JhonVelasquez/Embedded_system_Synchronize_Plant/Diagrams/RTOS_Flowchats_Architecture_diagrams/Flowchart_of_task_t_FG2_t_FG3.png

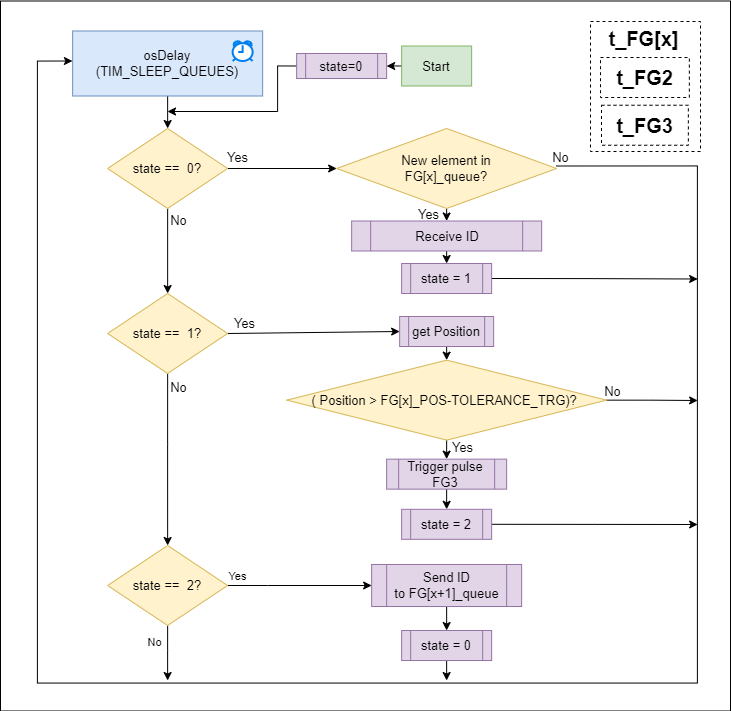
Diagrams/RTOS_Flowchats_Architecture_diagrams/Flowchart_of_task_t_FG2_t_FG3.png
