JhonVelasquez/Embedded_system_Synchronize_Plant/Diagrams/RTOS_Flowchats_Architecture_diagrams/Flowchart_of_task_t_RPI.png

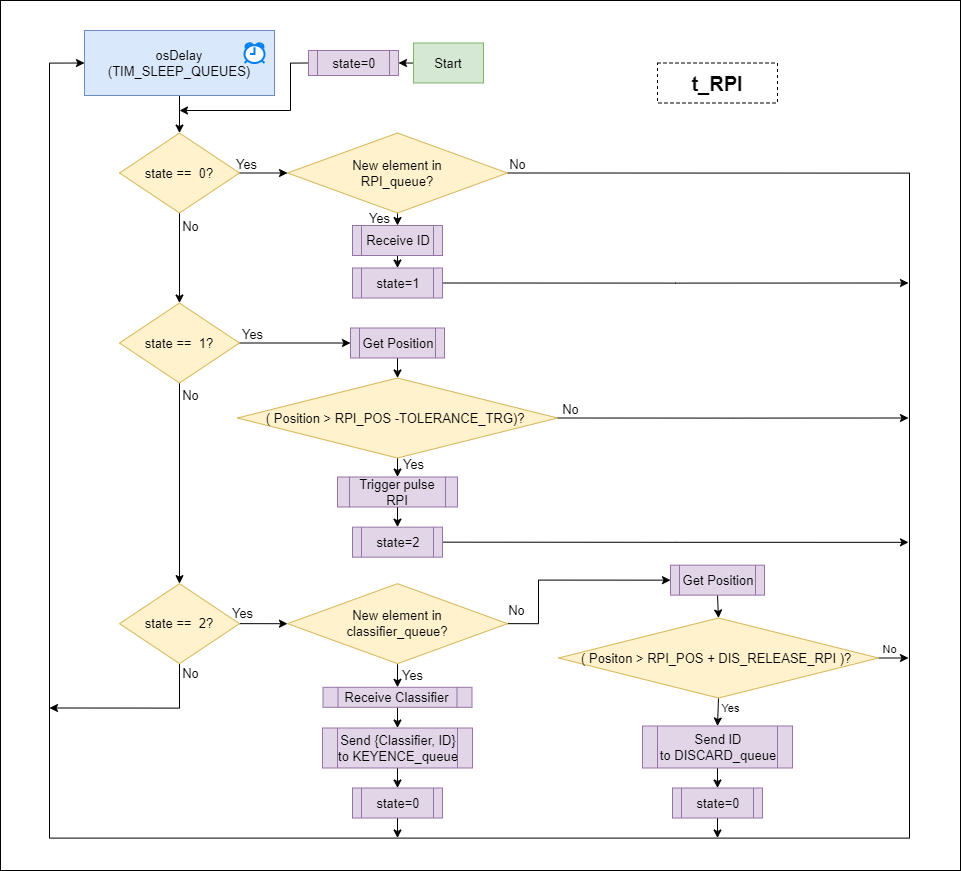
Diagrams/RTOS_Flowchats_Architecture_diagrams/Flowchart_of_task_t_RPI.png
