JhonVelasquez/Embedded_system_Synchronize_Plant/Diagrams/RTOS_Flowchats_Architecture_diagrams/RTOS_Command_Line_Interface_architechture.png

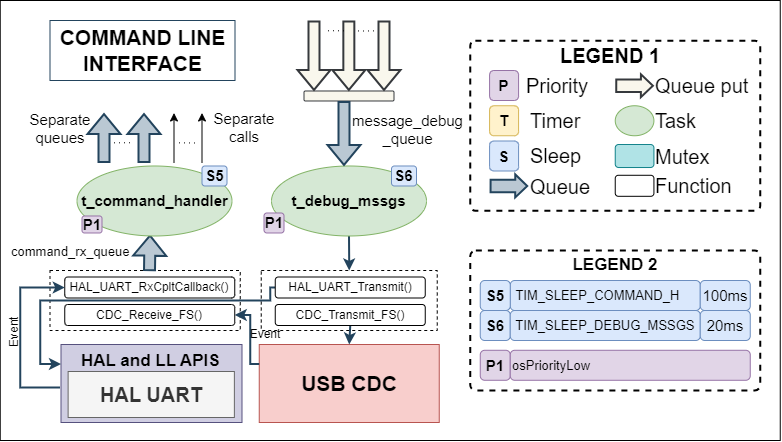
Diagrams/RTOS_Flowchats_Architecture_diagrams/RTOS_Command_Line_Interface_architechture.png
