JhonVelasquez/Embedded_system_Synchronize_Plant/KICAD_Schematich/jv_thesis/Ethernet_STM32_v1.png

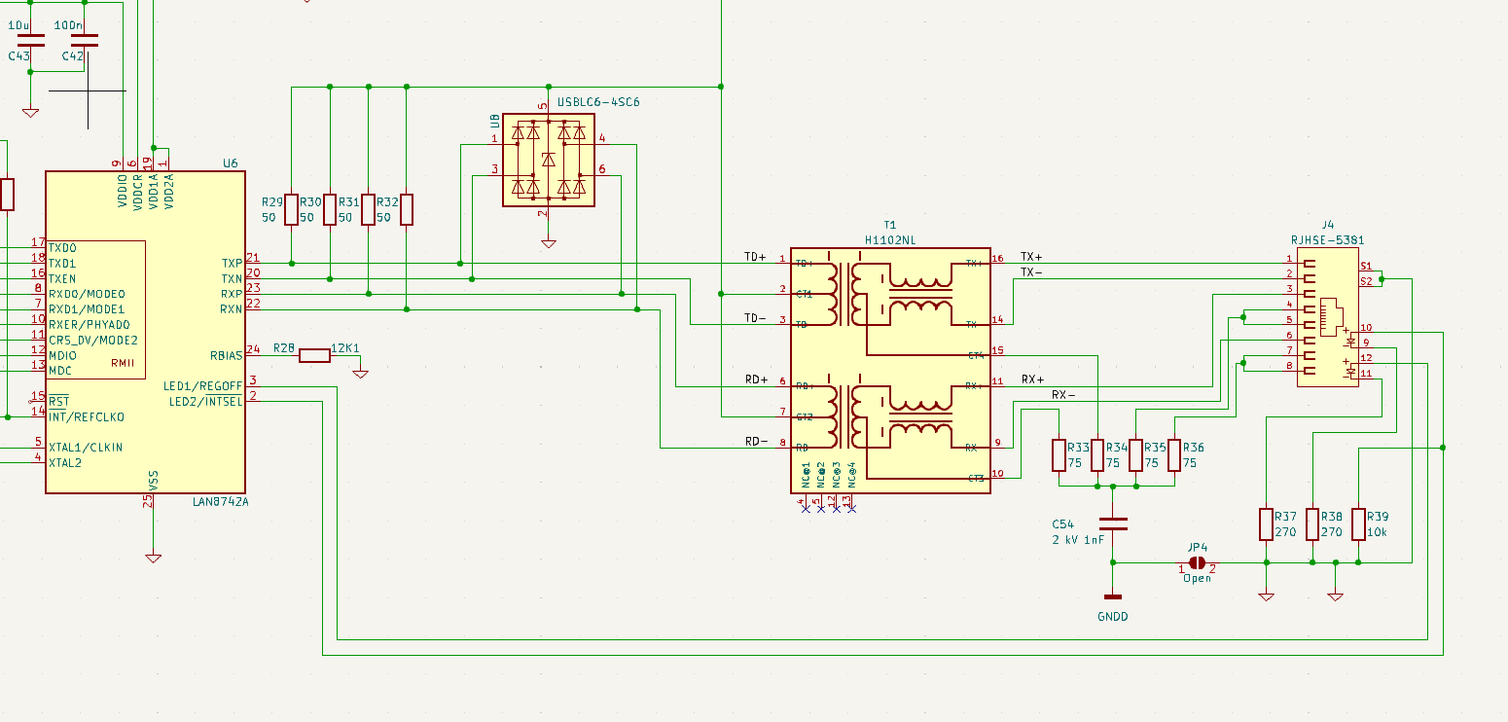
KICAD_Schematich/jv_thesis/Ethernet_STM32_v1.png
