JhonVelasquez/Embedded_system_Synchronize_Plant/KICAD_Schematich/jv_thesis/jv_thesis.kicad_sch

## KiCad design KICAD_Schematich/jv_thesis/jv_thesis.kicad_sch (2023-09-27)

Schematic: jv_thesis.kicad_sch

Parts:
C1, C2, C3, C4, C5, C6, C7, C8, C9, C10, C11, C12, C14, C27, C29, C42, C46, C47, C48, C49, C50, C51, C53, C54, C55, C59, C60, C63: 100n; C_0805_2012Metric_Pad1.18x1.45mm_HandSolder
C13, C30, C43, C58, C64: 10u; C_0805_2012Metric_Pad1.18x1.45mm_HandSolder
C15, C18, C28, C45, C56, C61, C62: 1u; C_0805_2012Metric_Pad1.18x1.45mm_HandSolder
C16, C17: 2.2u; C_0805_2012Metric_Pad1.18x1.45mm_HandSolder
C31, C41: 16p; CBR06C160F5GAC
C32, C40: 30p; CAP_600S0R1AT250XT_ATC
C33, C35, C36, C39: 10u-pol; CP_EIA-3216-18_Kemet-A_Pad1.58x1.35mm_HandSolder
C34: 20u (25v)-pol; CP_Elec_8x6.2
C37: 1u; C_1206_3216Metric_Pad1.33x1.80mm_HandSolder
C38: 4.7u; C_1812_4532Metric_Pad1.57x3.40mm_HandSolder
C44: 470p; C_0805_2012Metric_Pad1.18x1.45mm_HandSolder
CRYSTAL1: ECS-80-18-33-JGN-TR
CRYSTAL2: SXT21422AA07-25.000MT; SXT21422AA07_25_000M; PARTREV N/A
D1, D2, D3, D6: L_GREEN; D_0805_2012Metric_Pad1.15x1.40mm_HandSolder
D4: BAT60A; D_SOD-323_HandSoldering
D5: L_RED; D_0805_2012Metric_Pad1.15x1.40mm_HandSolder
D7: L_BLUE; D_0805_2012Metric_Pad1.15x1.40mm_HandSolder
F1: ERBRG2R50V; Fuse_1206_3216Metric_Pad1.42x1.75mm_HandSolder
FB1, FB2: 120R; L_0805_2012Metric_Pad1.15x1.40mm_HandSolder
H1, H2, H3, H4: MH; MountingHole_3.2mm_M3_Pad_Via
J1: 10118194-0001LF; USB_Micro_B_Female_10118194-0001LF; MPN 10118194-0001LF; Digi-Key_PN 609-4618-1-ND
J2, J5, J7, J8: Conn_01x02; PinSocket_1x02_P2.54mm_Vertical
J3: Conn_01x06; PinSocket_1x06_P2.54mm_Vertical
J4, J6: Conn_02x03; PinSocket_2x03_P2.54mm_Vertical
J9: 2000-1-2-41-00-BK; HDMI_A_Female_2000-1-2-41-00-BK; MPN 2000-1-2-41-00-BK; Digi-Key_PN 1175-1703-ND
J10: USB-A1HSB6
J11: THD-20-R; PinHeader_2x20_P2.54mm_Vertical; Part Description PinHeader_2x20_P2.54mm_Vertical
J12: ARJM11C7-502-AB-ER2-T; PARTREV 04.22.2019
J13: Keyence_1; 284512-2
J14: Keyence_2; 284512-2
J15: Keyence_3; 284512-2
J16: Keyence_4; 284512-2
J17, J18, J19: Conn_01x03; TerminalBlock_MetzConnect_Type059_RT06303HBWC_1x03_P3.50mm_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
J20, J21, J22, J27, J28: 284512-2
J23: Keyence_5; 284512-2
J24, J29, J30: Keyence_6; 284512-2
J25: Power_24V; 284512-2
J31: Conn_01x03; PinHeader_1x03_P2.54mm_Vertical
JP1, JP2, JP3, JP4, JP5, JP6, JP7, JP13, JP14, JP16, JP19, JP20, JP21, JP22, JP23, JP24, JP25, JP26, JP27, JP28, JP29, JP30: Open; SolderJumper-2_P1.3mm_Open_RoundedPad1.0x1.5mm
JP8, JP9, JP10, JP15, JP18: Closed; SolderJumper-2_P1.3mm_Bridged_RoundedPad1.0x1.5mm
Module1: ComputeModule4-CM4; Raspberry-Pi-4-Compute-Module
Q1: BC847; SOT-323_SC-70_Handsoldering
R1, R6, R33, R87: 10k; R_0805_2012Metric_Pad1.20x1.40mm_HandSolder
R2, R3, R36, R38, R40, R41, R49, R50, R51, R52, R57, R58, R59, R60, R68, R69, R74, R77: 2.2k; R_0805_2012Metric_Pad1.20x1.40mm_HandSolder
R4, R35, R39, R42, R43, R45, R46, R47, R48, R53, R54, R55, R56, R63, R64, R65, R66, R67: 210; R_0805_2012Metric_Pad1.20x1.40mm_HandSolder
R5: 1K; R_0805_2012Metric_Pad1.20x1.40mm_HandSolder
R7, R8: 4.7k; R_0805_2012Metric_Pad1.20x1.40mm_HandSolder
R9: 100; R_0805_2012Metric_Pad1.20x1.40mm_HandSolder
R10, R11, R12, R13: 22; R_0805_2012Metric_Pad1.20x1.40mm_HandSolder
R14: 47K; R_0805_2012Metric_Pad1.20x1.40mm_HandSolder
R15: 47k; R_0805_2012Metric_Pad1.20x1.40mm_HandSolder
R16: 22k; R_0805_2012Metric_Pad1.20x1.40mm_HandSolder
R17, R70, R72, R75, R78, R81: 330; R_0805_2012Metric_Pad1.20x1.40mm_HandSolder
R18, R19, R21, R22: 33; R_0805_2012Metric_Pad1.20x1.40mm_HandSolder
R20, R23, R24, R25, R27: 10K; R_0805_2012Metric_Pad1.20x1.40mm_HandSolder
R26: 1K5; R_0805_2012Metric_Pad1.20x1.40mm_HandSolder
R28: 12K1; R_0805_2012Metric_Pad1.20x1.40mm_HandSolder
R29, R30, R31, R32: 49.9; R_0805_2012Metric_Pad1.20x1.40mm_HandSolder
R34, R37: 270; R_0805_2012Metric_Pad1.20x1.40mm_HandSolder
R44, R61, R71, R73, R76, R79: 470; R_0805_2012Metric_Pad1.20x1.40mm_HandSolder
R62, R80, R82: 1k; R_0805_2012Metric_Pad1.20x1.40mm_HandSolder
SW1: RST; SW_SPST_Omron_B3FS-101xP
SW3: ESB-33535A; ESB_33535A
U1: STM32F746ZETx; LQFP-144_20x20mm_P0.5mm
U2, U9, U13: RT9742SNGV; SOT-23_Handsoldering; Part Description Power Switch/Driver 1:1 N-Channel 500mA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
U3: ARJM11A3-009-AB-ER2-T
U4: LD39050PU33R; DIGI-KEY_PART_NUMBER 497-8716-1-ND
U5, U7, U8, U10, U12: USBLC6-4SC6; SOT-23-6
U6: LAN8742A; VQFN-24-1EP_4x4mm_P0.5mm_EP2.45x2.45mm_ThermalVias
U11: EC5DAW; Converter_DCDC_EC5DAW_THT
U14, U17, U19: LTV-847; DIP-16_W7.62mm
U15, U16, U18: HCPL2630M

Connections:
3V3_F: C59.1, C61.1, J4.2, U4.4 (VOUT)
3V3_PER: C43.1, C60.1, FB2.2, J2.2, JP20.2 (B), JP23.2 (B), JP26.2 (B), JP29.2 (B), R4.1, R17.2, R23.1, R24.1, R25.1, R26.1, R27.1, R35.1, R39.1, R42.1, R43.1, R63.1, U6.9 (VDDIO), U12.5 (VBUS), U15.8 (VCC), U16.8 (VCC), U18.8 (VCC)
+3.3V: J2.1, J4.1, J4.3, J5.1, J7.1
+5V: C50.1, C62.1, J6.1, J6.3, J6.5, J8.1, JP18.1 (A), JP21.2 (B), JP24.2 (B), JP27.2 (B), JP30.2 (B), R5.1, U4.1 (EN), U4.6 (VIN)
+24V: J13.2, J14.2, J15.2, J16.2, J23.2, J24.2, J25.1, J29.2, J30.2, JP19.2 (B), JP22.2 (B), JP25.2 (B), JP28.2 (B), R49.2, R50.2, R51.2, R52.2, R57.2, R58.2, R59.2, R60.2
BOOT0: R1.1, SW3.5, U1.138 (BOOT0)
CM4_3V3: D1.2 (A), J7.2, J11.1, J11.17, J12.L1 (LED-L_A_GRN), J12.L3 (LED-R_A_YLW), U5.5 (VBUS), U7.5 (VBUS), U10.5 (VBUS)
CM4_5V: C58.1, C64.1, J8.2, J11.2, J11.4, JP4.1 (A), JP7.1 (A), JP18.2 (B), Module1.77 (+5v_(Input)), Module1.79 (+5v_(Input)), Module1.81 (+5v_(Input)), Module1.83 (+5v_(Input)), Module1.85 (+5v_(Input)), Module1.87 (+5v_(Input)), U9.1 (IN), U13.1 (IN)
CM4_RXD0: J11.10, JP13.2 (B), Module1.51 (GPIO15)
CM4_RXD3: J11.29, JP10.2 (B), Module1.34 (GPIO5)
CM4_RXD4: J11.21, Module1.40 (GPIO9)
CM4_TXD0: J11.8, JP14.2 (B), Module1.55 (GPIO14)
CM4_TXD3: J11.7, JP9.2 (B), Module1.54 (GPIO4)
CM4_TXD4: J11.24, Module1.39 (GPIO8)
CM4_USB_DM_-: J10.2, Module1.103 (USB2_N), U5.1 (I/O1)
CM4_USB_DP_+: J10.3, Module1.105 (USB2_P), U5.4 (I/O3)
E3V3: J4.4, J22.1
E5V: J6.4, J21.1
ENC_24V_1: J17.1, R2.1
ENC_24V_2: J17.2, R3.1
ENC_24V_3: J18.1, R36.1
ENC_24V_4: J18.2, R38.1
ENC_24V_5: J19.1, R40.1
ENC_24V_6: J19.2, R41.1
ENC_GPIO_1: R4.2, U1.75 (PB14), U15.7 (VO1)
ENC_GPIO_2: R35.2, U1.76 (PB15), U15.6 (VO2)
ENC_GPIO_3: R39.2, U1.79 (PD10), U16.7 (VO1)
ENC_GPIO_4: R43.2, U1.80 (PD11), U16.6 (VO2)
ENC_GPIO_5: R42.2, U1.81 (PD12), U18.7 (VO1)
ENC_GPIO_6: R63.2, U1.82 (PD13), U18.6 (VO2)
ETH_CRS_DV: R21.1, U1.43 (PA7)
ETH_LEDG: Module1.17 (Ethernet_nLED2(3.3v)), R44.1
ETH_LEDY: Module1.15 (Ethernet_nLED3(3.3v)), R61.1
ETH_MDC: U1.27 (PC1), U6.13 (MDC)
ETH_MDIO: R26.2, U1.36 (PA2), U6.12 (MDIO)
ETH_REF_CLK: R22.1, U1.35 (PA1)
ETH_RXD0: R18.1, U1.44 (PC4)
ETH_RXD1: R19.1, U1.45 (PC5)
ETH_TXD0: U1.128 (PG13), U6.17 (TXD0)
ETH_TXD1: U1.74 (PB13), U6.18 (TXD1)
ETH_TX_EN: U1.126 (PG11), U6.16 (TXEN)
GND: C1.2, C2.2, C3.2, C4.2, C5.2, C6.2, C7.2, C8.2, C9.2, C10.2, C11.2, C12.2, C13.2, C14.2, C15.2, C16.2, C17.2, C18.2, C27.2, C28.2, C29.2, C30.2, C31.1, C32.2, C33.2, C34.2, C35.2, C36.2, C37.2, C38.2, C39.2, C40.1, C41.2, C42.2, C43.2, C44.2, C45.2, C46.2, C47.2, C48.2, C49.2, C50.2, C51.1, C53.2, C54.2, C55.2, C56.2, C58.2, C59.2, C60.2, C61.2, C62.2, C63.2, C64.2, CRYSTAL1.2 (GND), CRYSTAL1.4 (GND), CRYSTAL2.2 (GND), CRYSTAL2.4 (GND), D2.1 (K), H1.1, H2.1, H3.1, H4.1, J1.5, J1.SH, J3.3, J9.2, J9.5, J9.8, J9.11, J9.17, J9.SH, J10.4, J11.6, J11.9, J11.14, J11.20, J11.25, J11.30, J11.34, J11.39, J12.S1 (SHIELD), J12.S2 (SHIELD), J20.2, J21.2, J22.2, J31.3, JP6.1 (A), Module1.1 (GND), Module1.2 (GND), Module1.7 (GND), Module1.8 (GND), Module1.13 (GND), Module1.14 (GND), Module1.22 (GND), Module1.23 (GND), Module1.33 (GND), Module1.59 (GND), Module1.60 (GND), Module1.65 (GND), Module1.66 (GND), Module1.71 (GND), Module1.74 (GND), Module1.98 (GND), Module1.101 (USB_OTG_ID), Module1.107 (GND), Module1.108 (GND), Module1.113 (GND), Module1.114 (GND), Module1.119 (GND), Module1.120 (GND), Module1.125 (GND), Module1.126 (GND), Module1.131 (GND), Module1.132 (GND), Module1.137 (GND), Module1.138 (GND), Module1.144 (GND), Module1.150 (GND), Module1.155 (GND), Module1.156 (GND), Module1.161 (GND), Module1.162 (GND), Module1.167 (GND), Module1.168 (GND), Module1.173 (GND), Module1.174 (GND), Module1.179 (GND), Module1.180 (GND), Module1.185 (GND), Module1.186 (GND), Module1.191 (GND), Module1.192 (GND), Module1.197 (GND), Module1.198 (GND), Q1.2 (E), R1.2, R6.2, R8.1, R14.2, R16.2, R20.1, R28.2, R33.2, R34.2, R37.2, R80.1, R81.1, R82.1, SW1.1, U1.16 (VSS), U1.31 (VSSA), U1.38 (VSS), U1.51 (VSS), U1.61 (VSS), U1.83 (VSS), U1.94 (VSS), U1.107 (VSS), U1.120 (VSS), U1.130 (VSS), U2.3 (GND), U3.8 (GND), U3.P$3 (GND), U3.P$4 (GND), U4.2 (GND), U4.7 (GND), U5.2 (GND), U6.25 (VSS), U7.2 (GND), U8.2 (GND), U9.3 (GND), U10.2 (GND), U11.1 (-Vin), U11.10 (-Vout), U12.2 (GND), U13.3 (GND), U14.2, U14.4, U14.6, U14.8, U15.5 (GND), U16.5 (GND), U17.2, U17.4, U17.6, U17.8, U18.5 (GND), U19.2, U19.4, U19.6, U19.8
GNDREF: J25.2, JP5.1 (A), U14.9, U14.11, U14.13, U14.15, U17.9, U17.11, U17.13, U17.15
GPIO2: J11.3, Module1.58 (GPIO2)
GPIO3: J11.5, Module1.56 (GPIO3)
GPIO6: J11.31, Module1.30 (GPIO6)
GPIO7: J11.26, Module1.37 (GPIO7)
GPIO10: J11.19, Module1.44 (GPIO10)
GPIO11: J11.23, Module1.38 (GPIO11)
GPIO12: J11.32, Module1.31 (GPIO12)
GPIO13: J11.33, Module1.28 (GPIO13)
GPIO16: J11.36, Module1.29 (GPIO16)
GPIO17: J11.11, Module1.50 (GPIO17)
GPIO18: J11.12, Module1.49 (GPIO18)
GPIO19: J11.35, Module1.26 (GPIO19)
GPIO20: J11.38, Module1.27 (GPIO20)
GPIO21: J11.40, Module1.25 (GPIO21)
GPIO22: J11.15, Module1.46 (GPIO22)
GPIO23: J11.16, Module1.47 (GPIO23)
GPIO24: J11.18, Module1.45 (GPIO24)
GPIO25: J11.22, Module1.41 (GPIO25)
GPIO26: J11.37, Module1.24 (GPIO26)
GPIO27: J11.13, Module1.48 (GPIO27)
HDMI0_CEC: J9.13, Module1.151 (HDMI0_CEC)
HDMI0_CK_N: J9.12, Module1.190 (HDMI0_CLK_N)
HDMI0_CK_P: J9.10, Module1.188 (HDMI0_CLK_P)
HDMI0_D0_N: J9.9, Module1.184 (HDMI0_TX0_N)
HDMI0_D0_P: J9.7, Module1.182 (HDMI0_TX0_P)
HDMI0_D1_N: J9.6, Module1.178 (HDMI0_TX1_N)
HDMI0_D1_P: J9.4, Module1.176 (HDMI0_TX1_P)
HDMI0_D2_N: J9.3, Module1.172 (HDMI0_TX2_N)
HDMI0_D2_P: J9.1, Module1.170 (HDMI0_TX2_P)
HDMI0_HOTPLUG: J9.19, Module1.153 (HDMI0_HOTPLUG)
HDMI0_SCL: J9.15, Module1.200 (HDMI0_SCL)
HDMI0_SDA: J9.16, Module1.199 (HDMI0_SDA)
ID_SC: J11.28, Module1.35 (ID_SC)
ID_SD: J11.27, Module1.36 (ID_SD)
INDICATOR_BLUE: D7.2 (A), U1.48 (PB2)
INDICATOR_GREEN: D6.2 (A), U1.47 (PB1)
INDICATOR_RED: D5.2 (A), U1.46 (PB0)
NRST: C29.1, JP15.1 (A), R12.1, R87.2, SW1.2, U1.25 (NRST)
unnamed: C32.1, CRYSTAL2.3 (OUT/IN), U6.4 (XTAL2)
unnamed: C35.1, C54.1, J9.18, JP4.2 (B), U9.2 (OUT)
unnamed: C36.1, C46.1, C47.1, C48.1, C49.1, C53.1, FB2.1, R29.1, R30.1, R31.1, R32.1, U3.4 (TXCT), U3.5 (RXCT), U6.1 (VDD2A), U6.19 (VDD1A), U8.5 (VBUS)
unnamed: C39.1, C63.1, J10.1, JP7.2 (B), U13.2 (OUT)
unnamed: C40.2, CRYSTAL2.1 (IN/OUT), U6.5 (XTAL1/CLKIN)
unnamed: C44.1, C45.1, U6.6 (VDDCR)
unnamed: C51.2, J12.5 (TRCT1), J12.6 (TRCT2)
unnamed: D1.1 (K), R62.2
unnamed: D2.2 (A), R5.2
unnamed: D3.1 (K), Q1.3 (C)
unnamed: D3.2 (A), R17.1
unnamed: D4.1 (K), R9.2
unnamed: D4.2 (A), JP2.2 (B), R6.1
unnamed: D5.1 (K), R80.2
unnamed: D6.1 (K), R81.2
unnamed: D7.1 (K), R82.2
unnamed: J12.L2 (LED-L_K_GRN), R44.2
unnamed: J12.L4 (LED-R_K_YLW), R61.2
unnamed: JP3.1 (A), R7.2
unnamed: JP5.2 (B), JP6.2 (B), U19.9, U19.11, U19.13, U19.15
unnamed: JP8.1 (A), Module1.84 (+3.3v_(Output))
unnamed: JP15.2 (B), U6.15 (~RST)
unnamed: JP16.1 (A), Module1.90 (+1.8v_(Output))
unnamed: JP8.2 (B), JP16.2 (B), Module1.78 (GPIO_VREF(1.8v/3.3v_Input))
unnamed: JP19.1 (A), R68.2
unnamed: JP20.1 (A), R72.2
unnamed: JP21.1 (A), R73.2
unnamed: JP22.1 (A), R69.2
unnamed: JP23.1 (A), R70.2
unnamed: JP24.1 (A), R71.2
unnamed: JP25.1 (A), R74.2
unnamed: JP26.1 (A), R75.2
unnamed: JP27.1 (A), R76.2
unnamed: JP28.1 (A), R77.2
unnamed: JP29.1 (A), R78.2
unnamed: JP30.1 (A), R79.2
unnamed: Module1.21 (PI_nLED_Activity), R62.1
unnamed: Q1.1 (B), R15.1, R16.1
unnamed: R2.2, U15.1 (A1)
unnamed: R3.2, U15.4 (A2)
unnamed: R7.1, R8.2, R9.1
unnamed: R18.2, R23.2, U6.8 (RXD0/MODE0)
unnamed: R19.2, R24.2, U6.7 (RXD1/MODE1)
unnamed: R20.2, U6.10 (RXER/PHYAD0)
unnamed: R21.2, R25.2, U6.11 (CRS_DV/MODE2)
unnamed: R22.2, R27.2, U6.14 (~INT/REFCLKO)
unnamed: R28.1, U6.24 (RBIAS)
unnamed: R33.1, U3.GRNA, U6.2 (LED2/~INTSEL)
unnamed: R34.1, U3.YLWC (YELC)
unnamed: R36.2, U16.1 (A1)
unnamed: R37.1, U3.GRNC
unnamed: R38.2, U16.4 (A2)
unnamed: R40.2, U18.1 (A1)
unnamed: R41.2, U18.4 (A2)
unnamed: R45.2, U14.1
unnamed: R46.2, U14.3
unnamed: R47.2, U14.5
unnamed: R48.2, U14.7
unnamed: R53.2, U17.1
unnamed: R54.2, U17.3
unnamed: R55.2, U17.5
unnamed: R56.2, U17.7
unnamed: R64.2, U19.1
unnamed: R65.2, U19.3
unnamed: R66.2, U19.5
unnamed: R67.2, U19.7
unnamed: U3.YLWA (YELA), U6.3 (LED1/REGOFF)
OSC_IN: C31.2, CRYSTAL1.1 (IN/OUT), U1.23 (PH0)
OSC_OUT: C41.1, CRYSTAL1.3 (OUT/IN), U1.24 (PH1)
RD+: R31.2, U3.3 (RD+), U6.23 (RXP), U8.6 (I/O4)
RD-: R32.2, U3.6 (RD-), U6.22 (RXN), U8.4 (I/O3)
REF_Lev1: J17.3, U15.2 (C1), U15.3 (C2)
REF_Lev2: J18.3, U16.2 (C1), U16.3 (C2)
REF_Lev3: J19.3, U18.2 (C1), U18.3 (C2)
SWCLK: R10.1, U1.109 (PA14)
SWDIO: R11.1, U1.105 (PA13)
SWO: R13.1, U1.133 (PB3)
SW_CLK: J3.2, R10.2
SW_DIO: J3.4, R11.2
SW_NRST: J3.5, R12.2
SW_SWO: J3.6, R13.2
SW_VDD: J3.1, JP2.1 (A)
TD+: R29.2, U3.1 (TD+), U6.21 (TXP), U8.3 (I/O2)
TD-: R30.2, U3.2 (TD-), U6.20 (TXN), U8.1 (I/O1)
TRD0_N: J12.2 (TRD1-), Module1.10 (Ethernet_Pair0_N), U7.6 (I/O4)
TRD0_P: J12.1 (TRD1+), Module1.12 (Ethernet_Pair0_P), U7.4 (I/O3)
TRD1_N: J12.4 (TRD2-), Module1.6 (Ethernet_Pair1_N), U7.3 (I/O2)
TRD1_P: J12.3 (TRD2+), Module1.4 (Ethernet_Pair1_P), U7.1 (I/O1)
TRD2_N: J12.8 (TRD3-), Module1.9 (Ethernet_Pair2_N), U10.4 (I/O3)
TRD2_P: J12.7 (TRD3+), Module1.11 (Ethernet_Pair2_P), U10.6 (I/O4)
TRD3_N: J12.10 (TRD4-), Module1.5 (Ethernet_Pair3_N), U10.3 (I/O2)
TRD3_P: J12.9 (TRD4+), Module1.3 (Ethernet_Pair3_P), U10.1 (I/O1)
TRIGGER_24V_1: J13.1, R49.1, U14.16
TRIGGER_24V_2: J14.1, R50.1, U14.14
TRIGGER_24V_3: J15.1, R51.1, U14.12
TRIGGER_24V_4: J16.1, R52.1, U14.10
TRIGGER_24V_5: J23.1, R57.1, U17.16
TRIGGER_24V_6: J24.1, R58.1, U17.14
TRIGGER_24V_7: J29.1, R59.1, U17.12
TRIGGER_24V_8: J30.1, R60.1, U17.10
TRIGGER_GPIO_1: R45.1, U1.68 (PE15)
TRIGGER_GPIO_2: R46.1, U1.67 (PE14)
TRIGGER_GPIO_3: R47.1, U1.66 (PE13)
TRIGGER_GPIO_4: R48.1, U1.65 (PE12)
TRIGGER_GPIO_5: R53.1, U1.64 (PE11)
TRIGGER_GPIO_6: R54.1, U1.63 (PE10)
TRIGGER_GPIO_7: R55.1, U1.60 (PE9)
TRIGGER_GPIO_8: R56.1, U1.59 (PE8)
TRIGGER_GPIO_9: R64.1, U1.5 (PE6)
TRIGGER_GPIO_10: R65.1, U1.4 (PE5)
TRIGGER_GPIO_11: R66.1, U1.3 (PE4)
TRIGGER_GPIO_12: R67.1, U1.2 (PE3)
TRIGGER_xxV_9: J27.1, R68.1, R72.1, R73.1, U19.16
TRIGGER_xxV_10: J27.2, R69.1, R70.1, R71.1, U19.14
TRIGGER_xxV_11: J28.1, R74.1, R75.1, R76.1, U19.12
TRIGGER_xxV_12: J28.2, R77.1, R78.1, R79.1, U19.10
U5V: C30.1, J1.1, JP1.1 (A), R15.2, U2.1 (IN)
U5V_F: C33.1, C42.1, J6.6, JP1.2 (B), U2.2 (OUT)
UART5_RX: JP9.1 (A), U1.116 (PD2)
UART5_TX: JP10.1 (A), U1.113 (PC12)
USART3_RX: J31.1, U1.78 (PD9)
USART3_TX: J31.2, U1.77 (PD8)
USART6_RX: JP14.1 (A), U1.97 (PC7)
USART6_TX: JP13.1 (A), U1.96 (PC6)
USB_DM_-: J1.2, U1.103 (PA11), U12.4 (I/O3)
USB_DP_+: J1.3, U1.104 (PA12), U12.1 (I/O1)
USB_ID: J1.4, R14.1
VCAP_1: C16.1, U1.71 (VCAP_1)
VCAP_2: C17.1, U1.106 (VCAP_2)
VDD: C1.1, C2.1, C3.1, C4.1, C5.1, C6.1, C7.1, C8.1, C9.1, C10.1, C11.1, C12.1, C13.1, C18.1, C27.1, C28.1, FB1.1, J5.2, JP3.2 (B), R87.1, SW3.6, U1.6 (VBAT), U1.17 (VDD), U1.30 (VDD), U1.39 (VDD), U1.52 (VDD), U1.62 (VDD), U1.72 (VDD), U1.84 (VDD), U1.95 (VDDUSB), U1.108 (VDD), U1.121 (VDD), U1.131 (VDD), U1.144 (VDD)
VDDA: C14.1, C15.1, C55.1, C56.1, FB1.2, U1.32 (VREF+), U1.33 (VDDA)
VIN: F1.1, J20.1
VIN_F: C37.1, J6.2, U11.9 (+Vout)
VinDC: C34.1, C38.1, F1.2, U11.16 (+Vin)

Notes on the sheet:
TRIGGER GPIO - OUTPUT
POWER MANAGEMENT 5V
Serial Wire ST-LINK
3.3v to 24v
Optoisolated Outputs (Configurable)
CM4
Ethernet - MCU
HDMI - CM4
MOUNTING HOLES
Optoisolated Outputs
3.3v to +24v, 3V3 or +5V
Activity LED
Power Adaptation MCU
MCU
LED Indicators
RMII
Optoisolated Inputs
Micro USB - MCU
0.5A
EXTERNAL CONECTORS
POWER MANAGEMENT 3.3V
USB Type B - CM4
24v to 3.3v
SERIAL TO CM4
MCU - PERIPHERIALS
Ethernet - CM4
CM4 - 40-pin GPIO header (HAT connector)
